mattwilliamson/fennee/models/SpotMicroESP32_with_reinforced_shoulders_4937631/images/featured_preview_RearCAD1.png

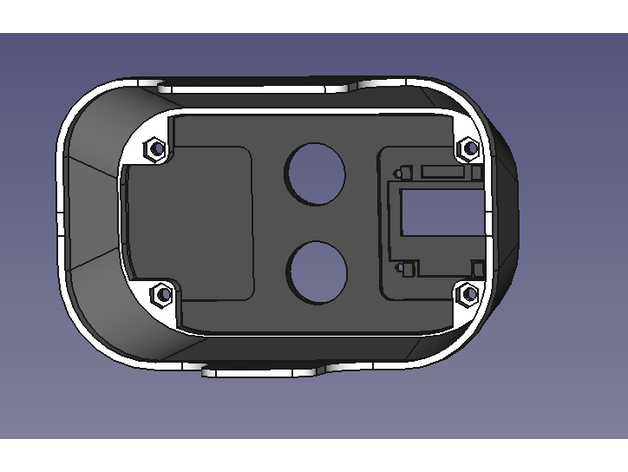
models/SpotMicroESP32_with_reinforced_shoulders_4937631/images/featured_preview_RearCAD1.png
