mattwilliamson/fennee/models/SpotMicroESP32_with_reinforced_shoulders_4937631/images/featured_preview_standing_with_shoulders_rear.png

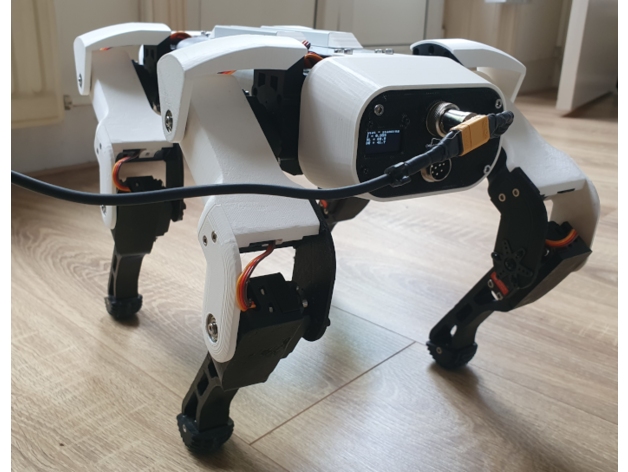
models/SpotMicroESP32_with_reinforced_shoulders_4937631/images/featured_preview_standing_with_shoulders_rear.png
