mattwilliamson/fennee/models/SpotMicroESP32_with_reinforced_shoulders_4937631/images/Shoulder_Cover.png

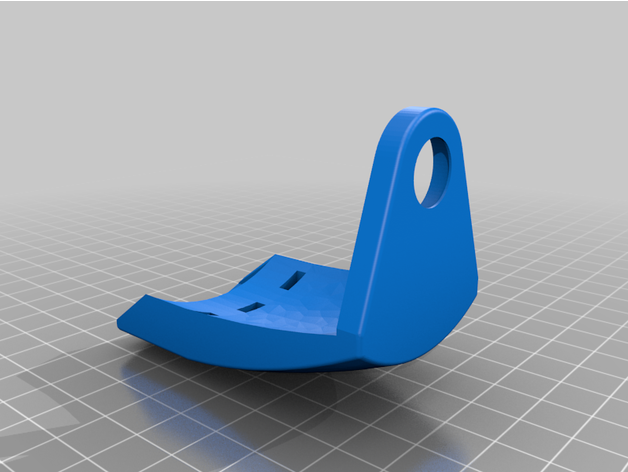
models/SpotMicroESP32_with_reinforced_shoulders_4937631/images/Shoulder_Cover.png
