mattwilliamson/fennee/models/SpotMicroESP32_with_reinforced_shoulders_4937631/images/Shoulder_Joint_Ball_Bearing_Pin_M3x8.png

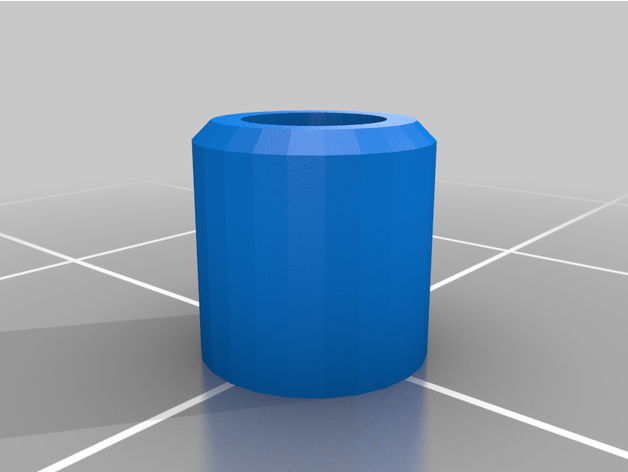
models/SpotMicroESP32_with_reinforced_shoulders_4937631/images/Shoulder_Joint_Ball_Bearing_Pin_M3x8.png
