mattwilliamson/fennee/models/SpotMicroESP32_with_reinforced_shoulders_4937631/images/Shoulder_Joint_Servo_Cap_Extended.png

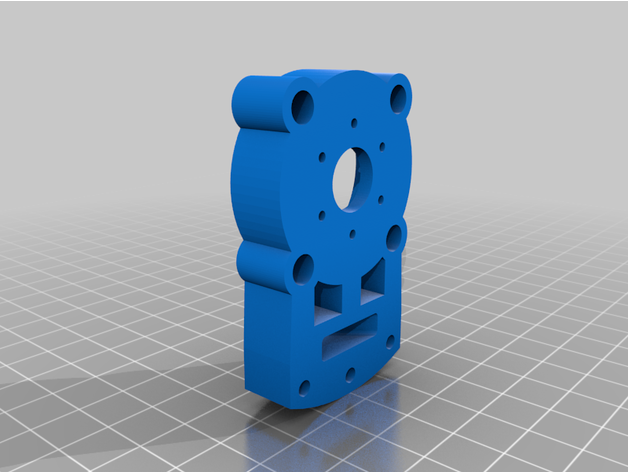
models/SpotMicroESP32_with_reinforced_shoulders_4937631/images/Shoulder_Joint_Servo_Cap_Extended.png
