mattwilliamson/fennee/models/SpotMicroESP32_with_reinforced_shoulders_4937631/images/Shoulder_Joint_Servomount_extended_BB.png

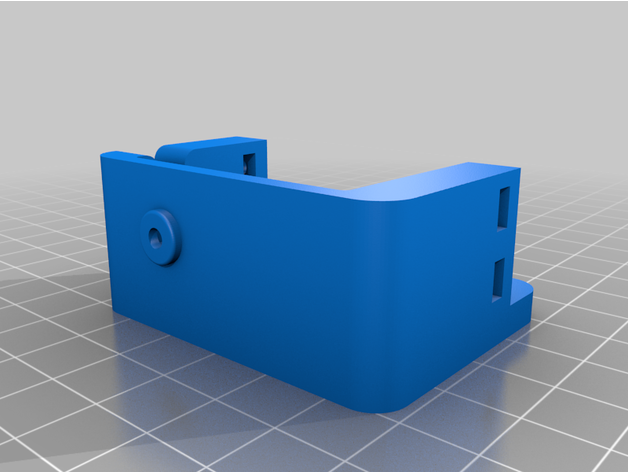
models/SpotMicroESP32_with_reinforced_shoulders_4937631/images/Shoulder_Joint_Servomount_extended_BB.png
