mattwilliamson/fennee/models/Rear_Cover/Rear_Cover_Shell_Medium.FCStd

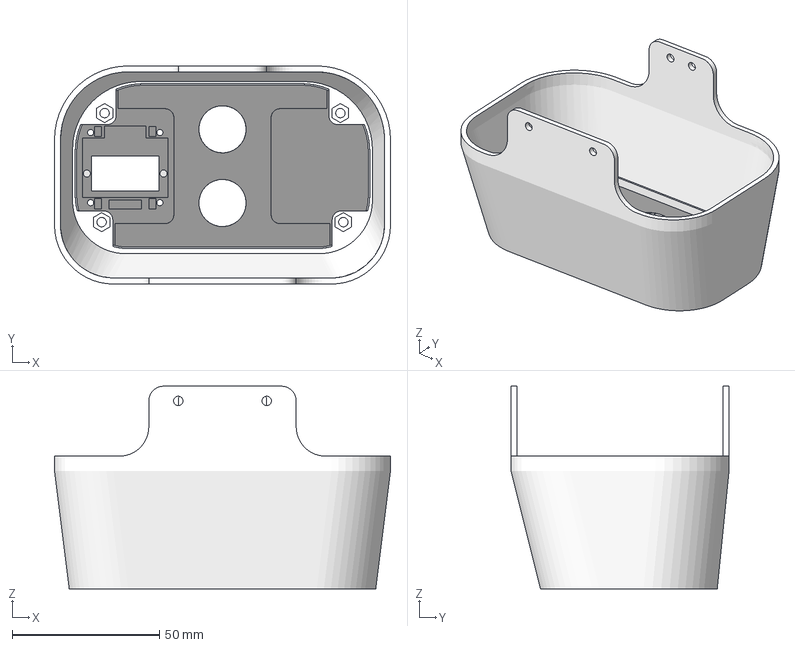
[picture p30: CAD file, 2023-06-12]
models/Rear_Cover/Rear_Cover_Shell_Medium.FCStd
114.0 x 74.0 x 68.7 mm
Rear_Cover_Shell_medium
Rear_Cover_Plate_medium
Power Plug Hole (Meshed)
