mattwilliamson/fennee/models/SpotMicroESP32_with_reinforced_shoulders_4937631/files/Shoulder_Joint_Servomount_extended_BB.stl

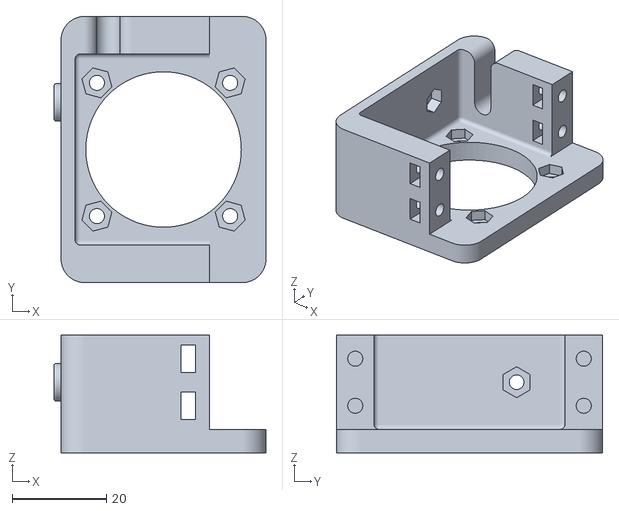
[picture p31: CAD file, 2023-05-03]
models/SpotMicroESP32_with_reinforced_shoulders_4937631/files/Shoulder_Joint_Servomount_extended_BB.stl
45.0 x 56.5 x 25.0
