mattwilliamson/fennee/models/top_cover/top_cover_back.stl

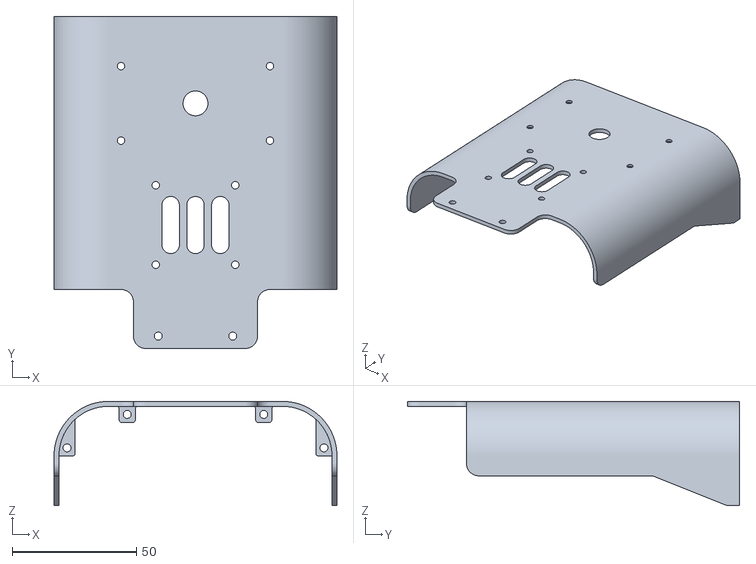
[picture p32: CAD file, 2023-05-14]
models/top_cover/top_cover_back.stl
114.0 x 133.8 x 42.0
