mattwilliamson/fennee/models/Wrist_35kg_servo/Wrist.FCStd

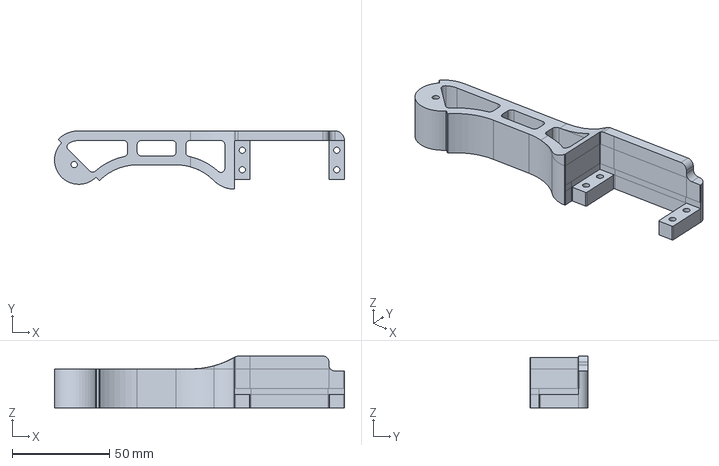
[picture p33: CAD file, 2023-06-16]
models/Wrist_35kg_servo/Wrist.FCStd
149.0 x 30.0 x 26.6 mm
