mattwilliamson/fennee/fennee_description/meshes/FreeCAD/SpotMicroAI_Bottom.FCStd

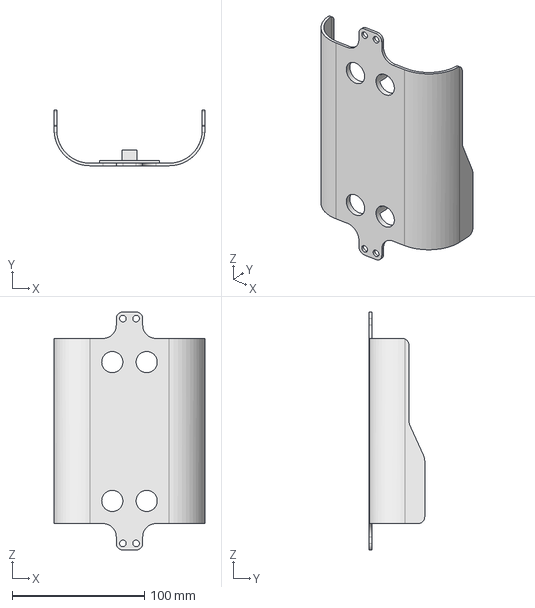
[picture p34: CAD file, 2023-04-16]
fennee_description/meshes/FreeCAD/SpotMicroAI_Bottom.FCStd
114.0 x 42.0 x 180.0 mm
