mattwilliamson/fennee/models/face/Front_Cover_oakdlite.FCStd

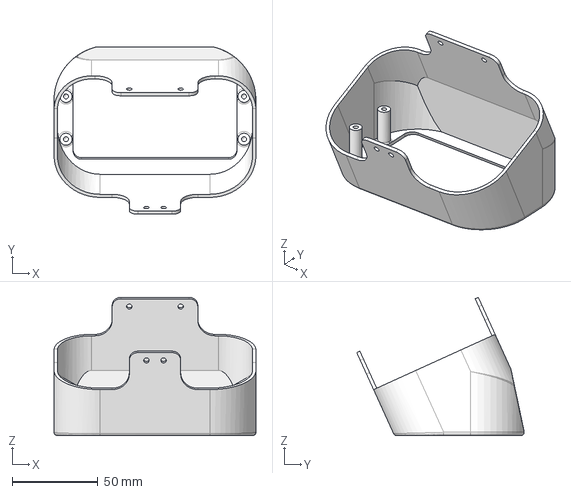
[picture p35: CAD file, 2023-05-17]
models/face/Front_Cover_oakdlite.FCStd
118.0 x 97.8 x 80.8 mm
