mattwilliamson/fennee/models/Rear_Cover/Rear_Cover_Plate_Medium.stl

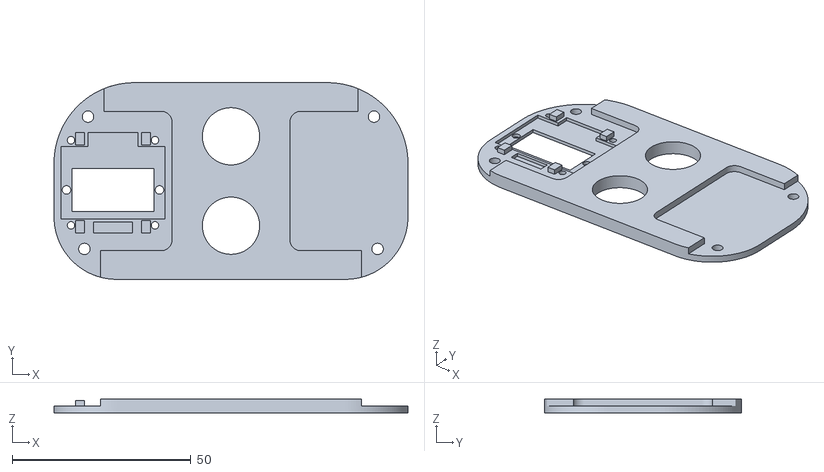
[picture p36: CAD file, 2023-06-12]
models/Rear_Cover/Rear_Cover_Plate_Medium.stl
99.0 x 55.0 x 4.00
