mattwilliamson/fennee/models/SpotMicroESP32_with_reinforced_shoulders_4937631/files/Shoulder_Joint_Servo_Cap_Extended.stl

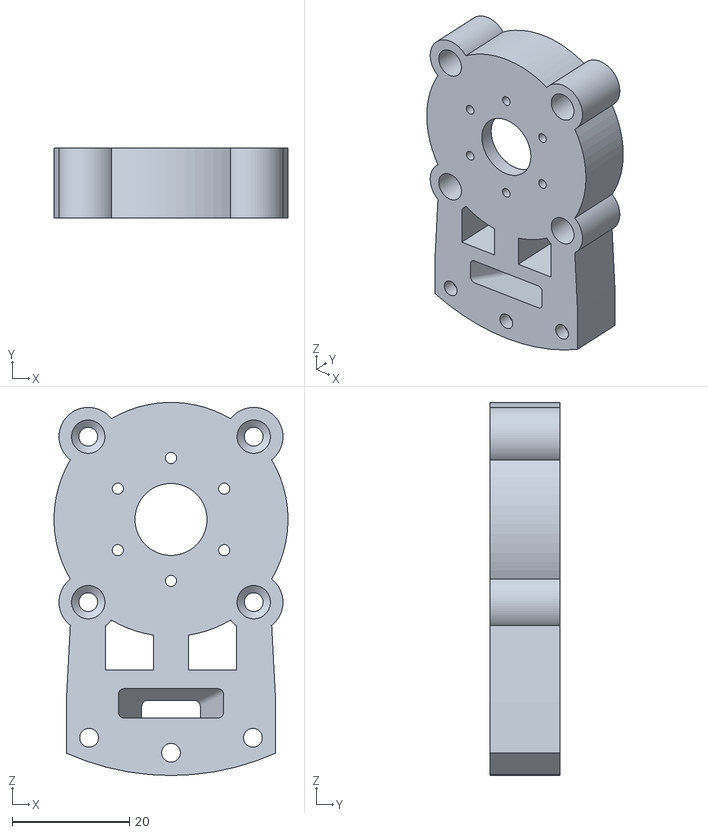
[picture p37: CAD file, 2023-05-03]
models/SpotMicroESP32_with_reinforced_shoulders_4937631/files/Shoulder_Joint_Servo_Cap_Extended.stl
40.0 x 12.0 x 63.8
