mattwilliamson/fennee/models/top_cover/top_cover_front.stl

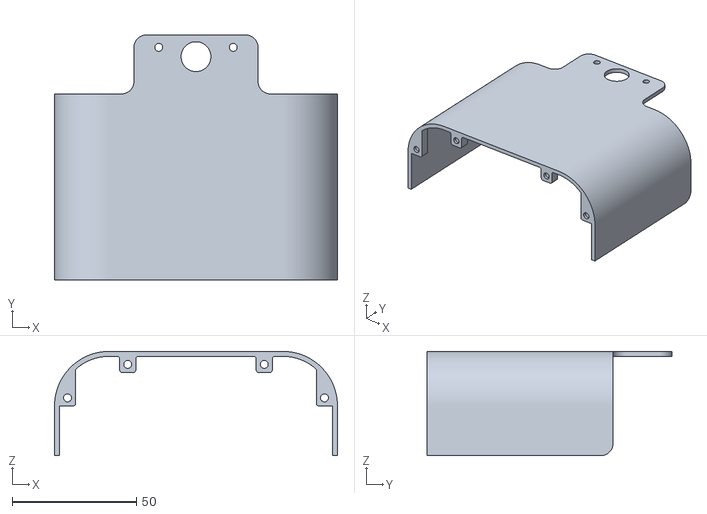
[picture p38: CAD file, 2023-05-14]
models/top_cover/top_cover_front.stl
114.0 x 98.8 x 42.0
