mattwilliamson/fennee/fennee_description/meshes/FreeCAD/SpotMicroAI_Top.FCStd

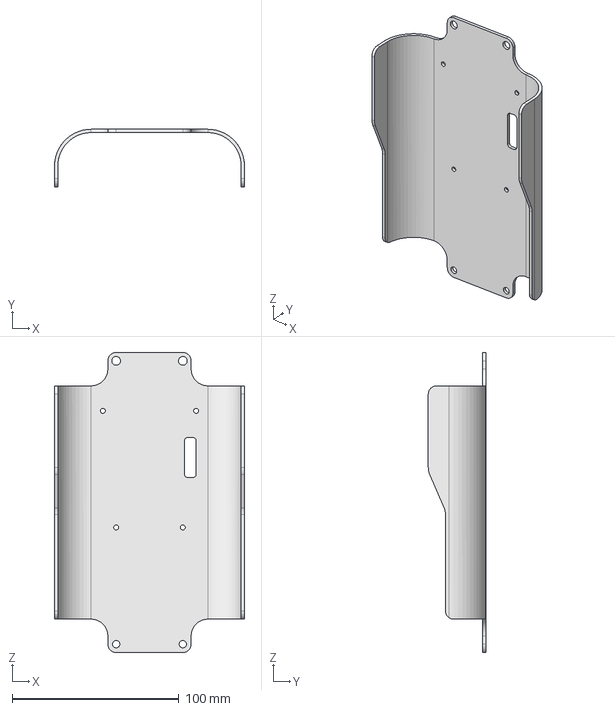
[picture p39: CAD file, 2023-04-16]
fennee_description/meshes/FreeCAD/SpotMicroAI_Top.FCStd
114.0 x 34.5 x 180.0 mm
