mattwilliamson/fennee/fennee_description/meshes/stl/R_side_plate.stl

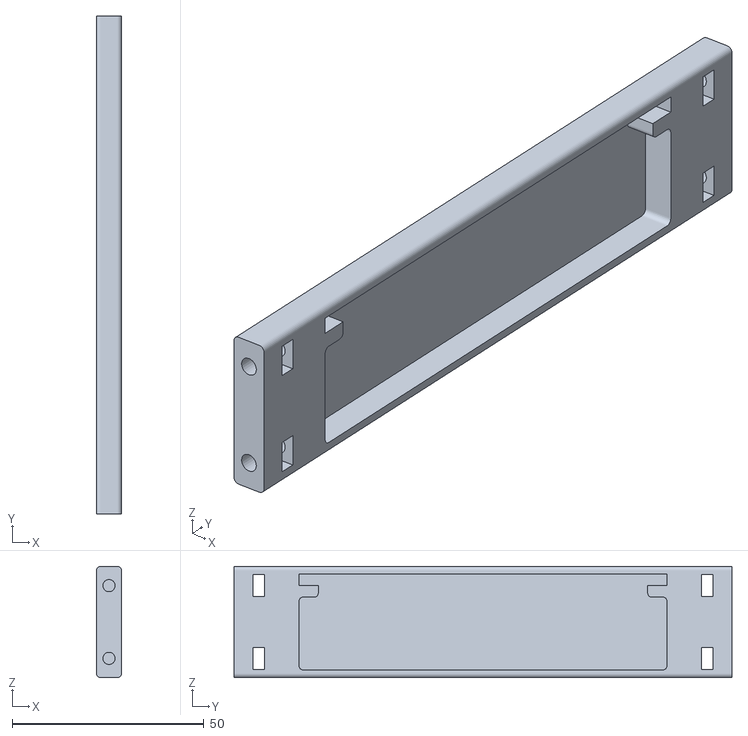
[picture p40: CAD file, 2023-04-16]
fennee_description/meshes/stl/R_side_plate.stl
6.50 x 130.0 x 29.0
