mattwilliamson/fennee/models/SpotMicroESP32_with_reinforced_shoulders_4937631/files/Rear_Cover_Shell_Medium.FCStd

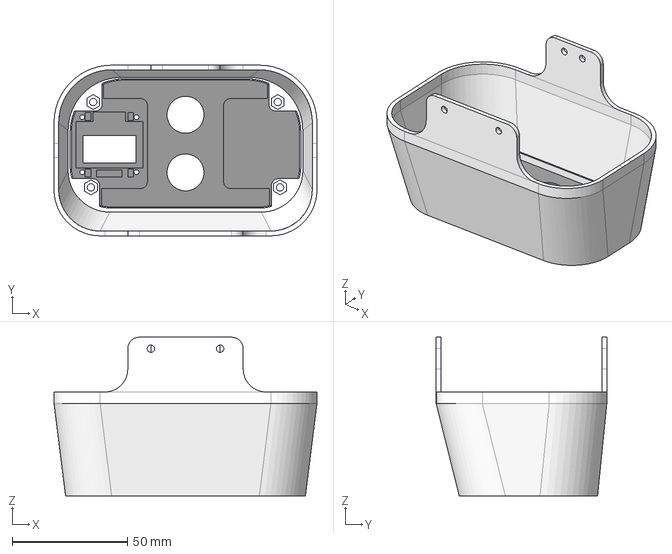
[picture p41: CAD file, 2023-05-03]
models/SpotMicroESP32_with_reinforced_shoulders_4937631/files/Rear_Cover_Shell_Medium.FCStd
114.0 x 74.0 x 68.7 mm
Rear_Cover_Shell_medium
Rear_Cover_Plate_medium
