mattwilliamson/fennee/fennee_description/meshes/FreeCAD/SpotMicroAI_AdditionalParts.FCStd

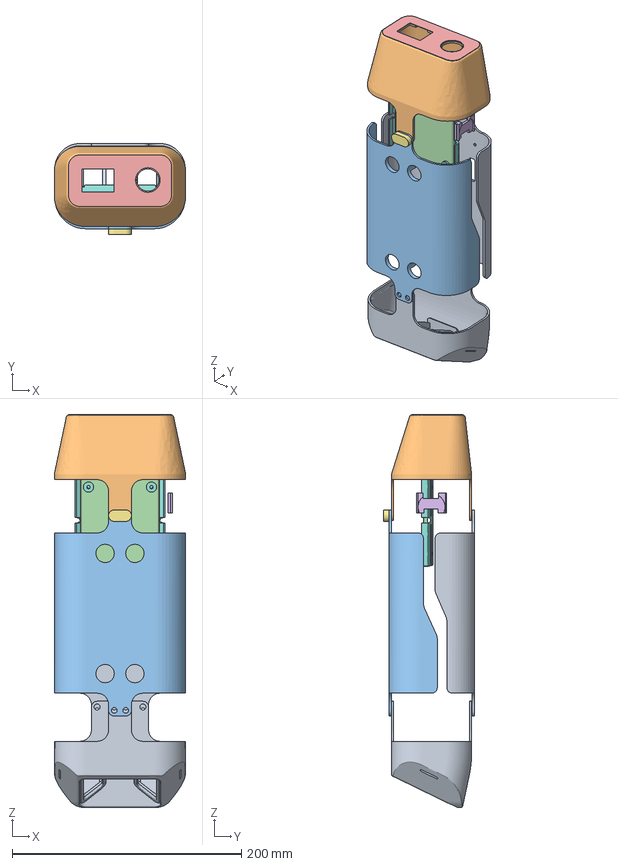
[picture p42: CAD file, 2023-04-16]
fennee_description/meshes/FreeCAD/SpotMicroAI_AdditionalParts.FCStd
114.8 x 79.5 x 343.2 mm
Top
Rear
Bottom
BatteryHolderHolder
rearlabel
LEDMount
ScrewGuard
F_cover
