mattwilliamson/fennee/fennee_description/meshes/stl/frontpart.stl

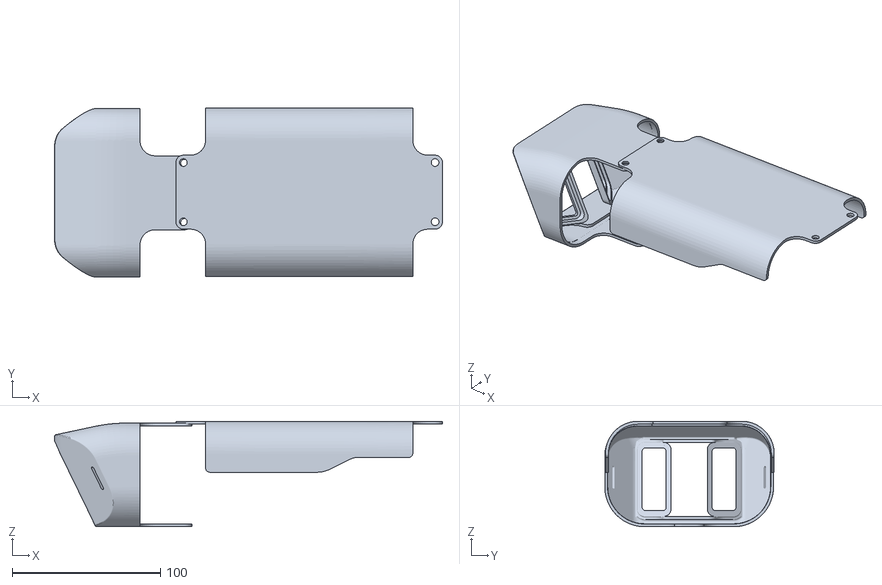
[picture p43: CAD file, 2023-04-16]
fennee_description/meshes/stl/frontpart.stl
262.0 x 114.5 x 71.2
