mattwilliamson/fennee/models/SpotMicroESP32_with_reinforced_shoulders_4937631/files/Shoulder_Joint_Ball_Bearing_Pin_M3x8.stl

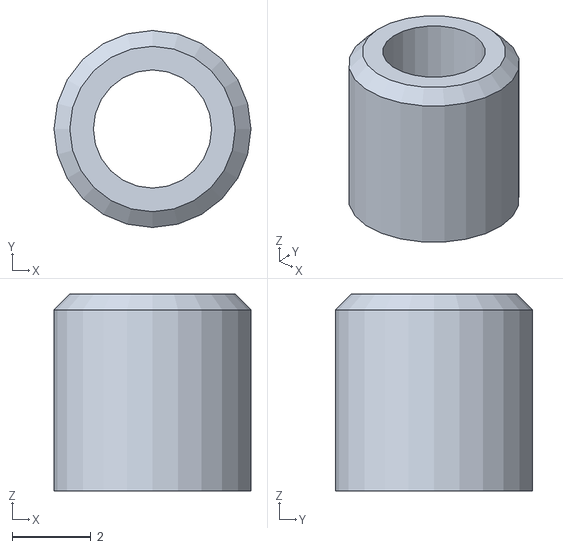
[picture p44: CAD file, 2023-05-03]
models/SpotMicroESP32_with_reinforced_shoulders_4937631/files/Shoulder_Joint_Ball_Bearing_Pin_M3x8.stl
5.00 x 5.00 x 5.00
