mattwilliamson/fennee/fennee_description/meshes/FreeCAD/SpotMicroAI_JetsonParts.FCStd

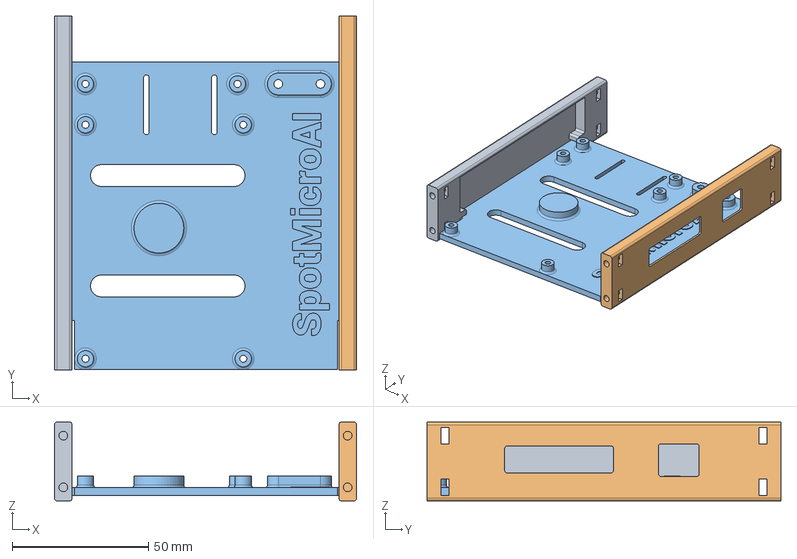
[picture p45: CAD file, 2023-04-16]
fennee_description/meshes/FreeCAD/SpotMicroAI_JetsonParts.FCStd
111.0 x 130.0 x 29.0 mm
rightSideplate
leftSideplate
JetsonPlateWithText
