mattwilliamson/fennee/fennee_description/meshes/stl/R_wrist.stl

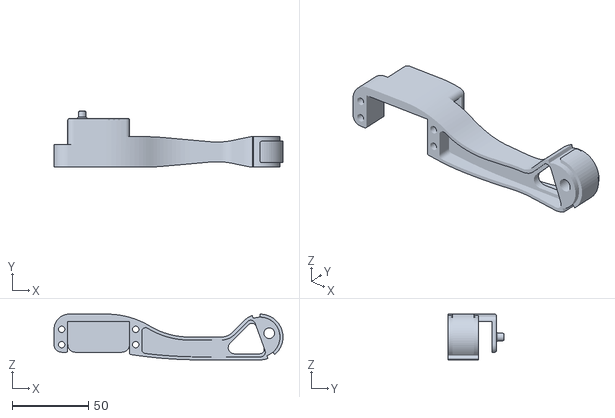
[picture p46: CAD file, 2023-04-16]
fennee_description/meshes/stl/R_wrist.stl
150.0 x 36.9 x 30.0
