mattwilliamson/fennee/fennee_description/meshes/stl/non-mega_T_cover.stl

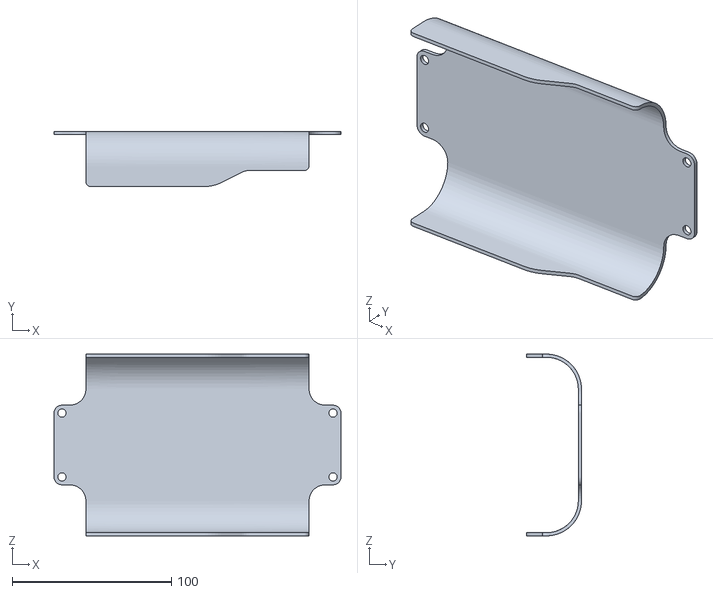
[picture p47: CAD file, 2023-04-16]
fennee_description/meshes/stl/non-mega_T_cover.stl
180.0 x 34.5 x 114.0
