mattwilliamson/fennee/models/SpotMicroESP32_with_reinforced_shoulders_4937631/files/Limb_Top_Shell_with_BB_hole.stl

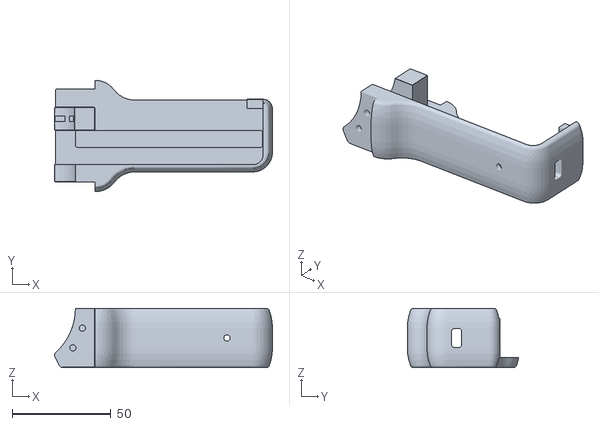
[picture p48: CAD file, 2023-05-03]
models/SpotMicroESP32_with_reinforced_shoulders_4937631/files/Limb_Top_Shell_with_BB_hole.stl
110.6 x 56.5 x 30.0
