mattwilliamson/fennee/models/SpotMicroESP32_with_reinforced_shoulders_4937631/files/Shoulder_Cover.stl

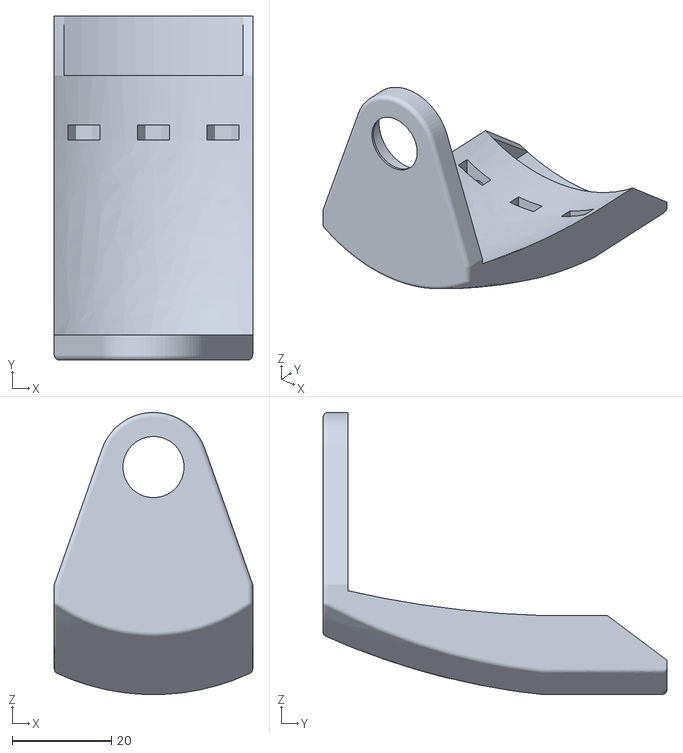
[picture p49: CAD file, 2023-05-03]
models/SpotMicroESP32_with_reinforced_shoulders_4937631/files/Shoulder_Cover.stl
40.0 x 69.3 x 56.8
