mattwilliamson/fennee/fennee_description/meshes/stl/jetson_sidepart.stl

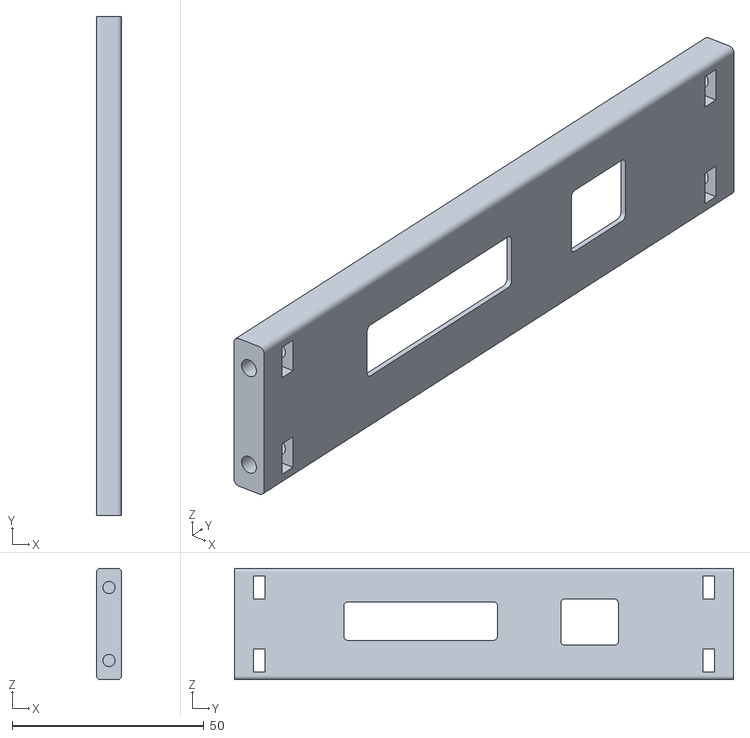
[picture p50: CAD file, 2023-04-16]
fennee_description/meshes/stl/jetson_sidepart.stl
6.50 x 130.0 x 29.0
