mattwilliamson/fennee/fennee_description/meshes/stl/lshoulder.stl

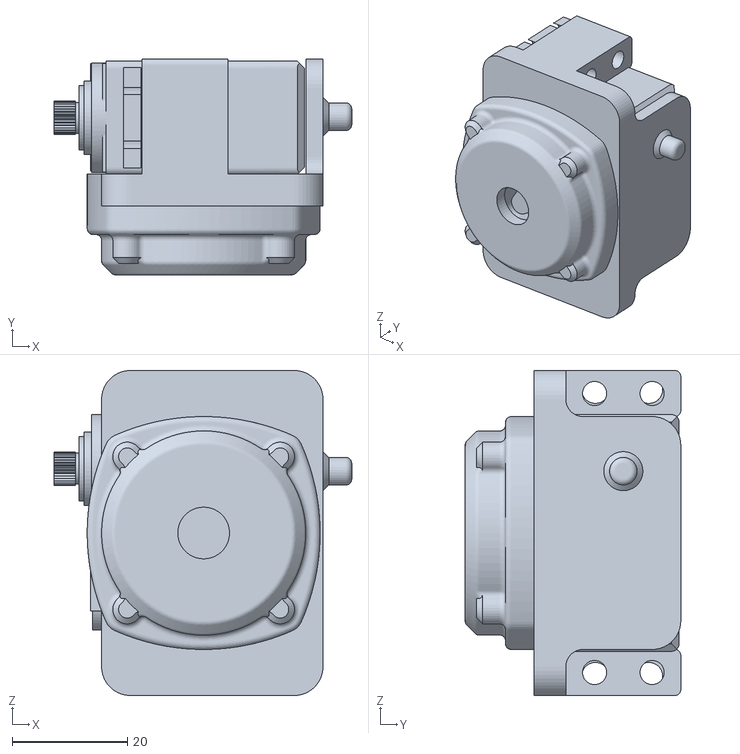
[picture p51: CAD file, 2023-04-16]
fennee_description/meshes/stl/lshoulder.stl
51.7 x 37.5 x 56.5
