mattwilliamson/fennee/fennee_description/meshes/stl/label.stl

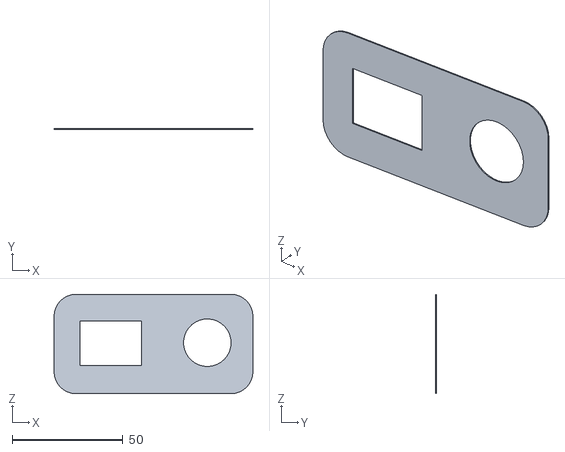
[picture p52: CAD file, 2023-04-16]
fennee_description/meshes/stl/label.stl
90.0 x 0.4 x 45.0
