mattwilliamson/fennee/fennee_description/meshes/stl/plate.stl

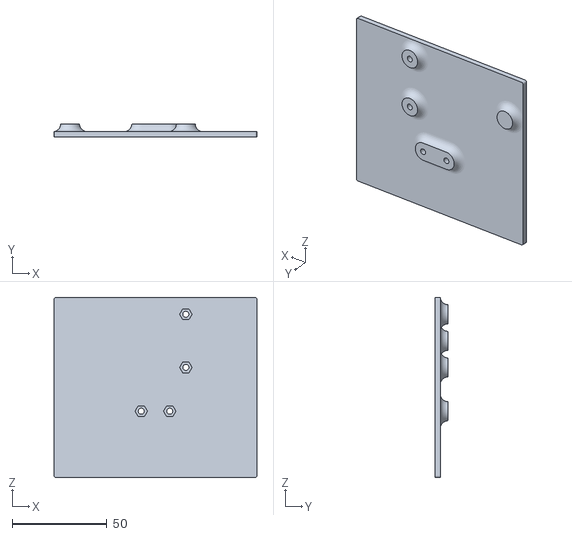
[picture p53: CAD file, 2023-04-16]
fennee_description/meshes/stl/plate.stl
107.0 x 7.00 x 95.0
