mattwilliamson/fennee/fennee_description/meshes/stl/F_cover.stl

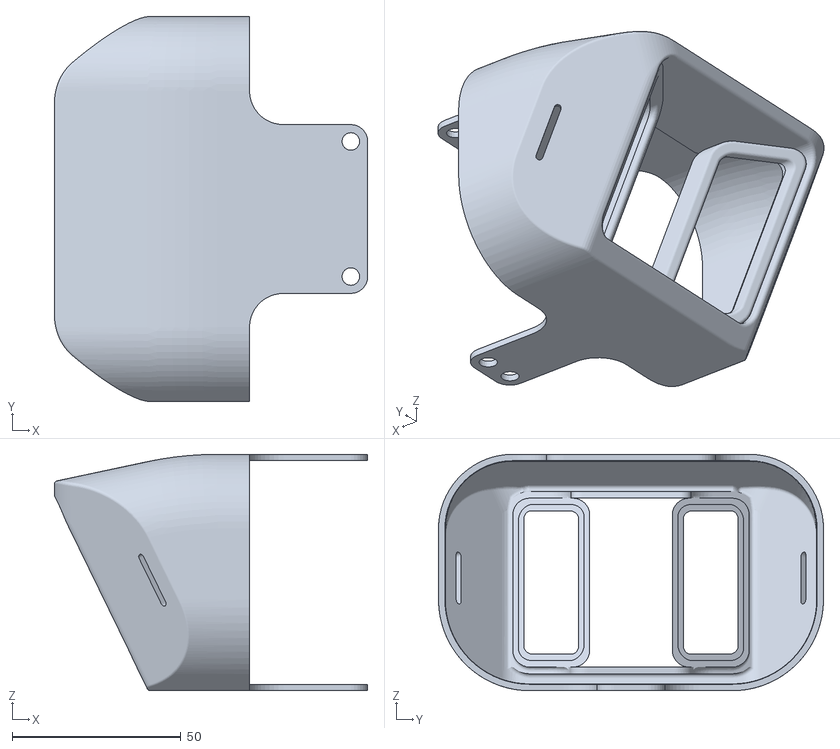
[picture p54: CAD file, 2023-04-16]
fennee_description/meshes/stl/F_cover.stl
92.8 x 114.0 x 70.0
