mattwilliamson/fennee/fennee_description/meshes/stl/R_cover.stl

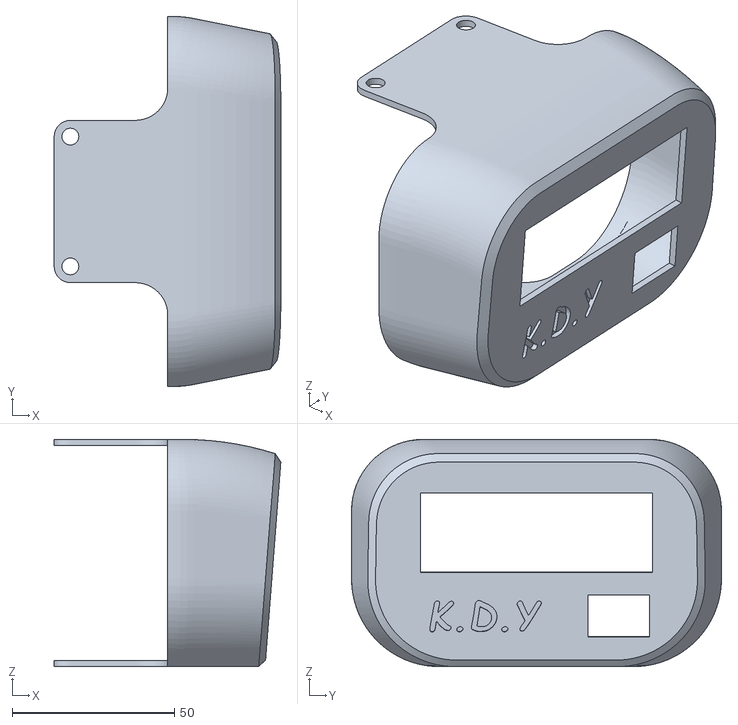
[picture p55: CAD file, 2023-04-16]
fennee_description/meshes/stl/R_cover.stl
69.8 x 114.0 x 70.0
