mattwilliamson/fennee/fennee_description/meshes/stl/ledholder.stl

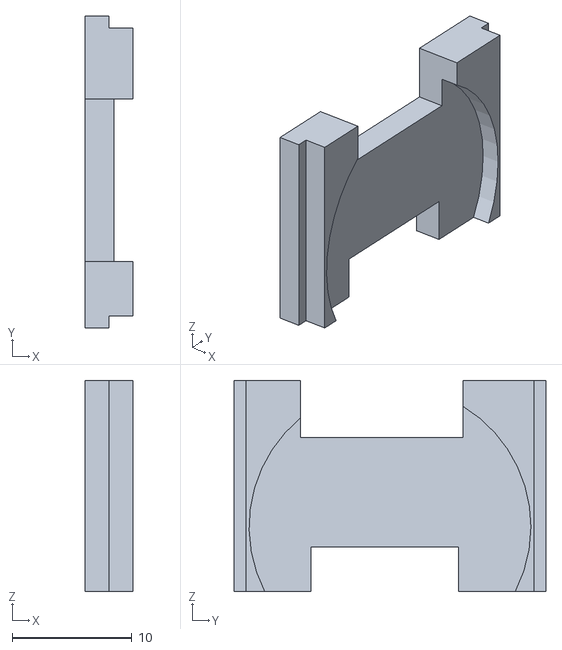
[picture p56: CAD file, 2023-04-16]
fennee_description/meshes/stl/ledholder.stl
4.00 x 26.0 x 17.6
