mattwilliamson/fennee/fennee_description/meshes/stl/F_shoulder.stl

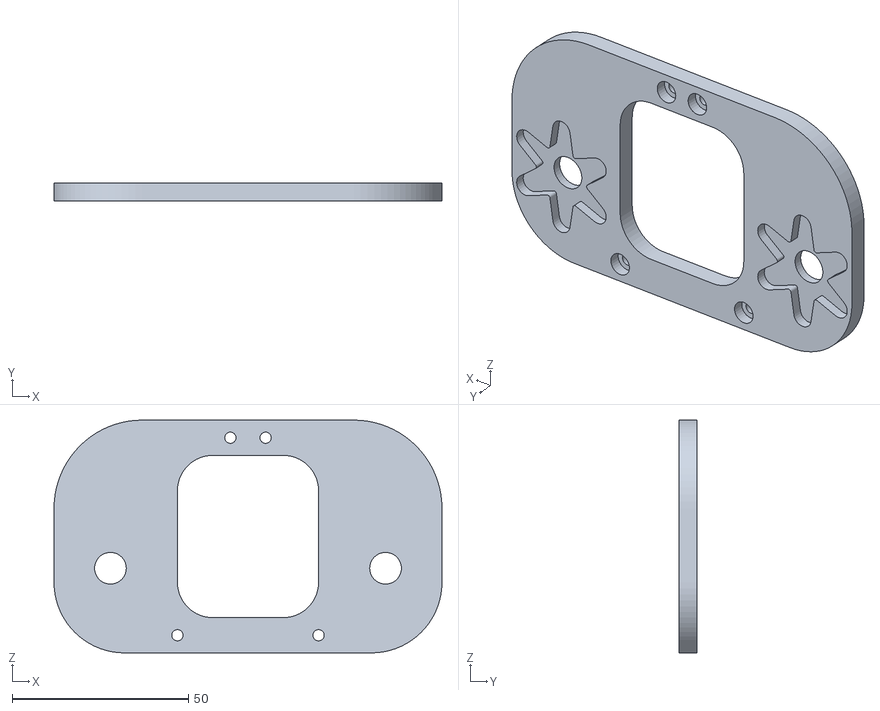
[picture p57: CAD file, 2023-04-16]
fennee_description/meshes/stl/F_shoulder.stl
110.0 x 5.00 x 66.0
