mattwilliamson/fennee/fennee_description/meshes/stl/lfoot.stl

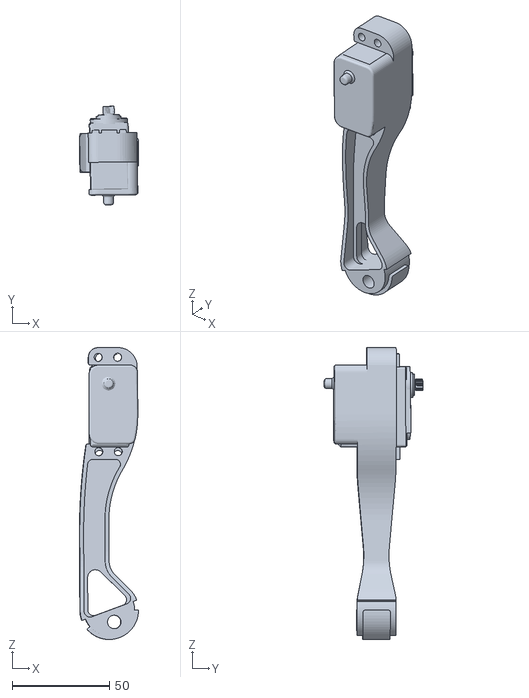
[picture p58: CAD file, 2023-04-16]
fennee_description/meshes/stl/lfoot.stl
30.4 x 50.7 x 150.0
