mattwilliamson/fennee/fennee_description/meshes/stl/batteryholder.stl

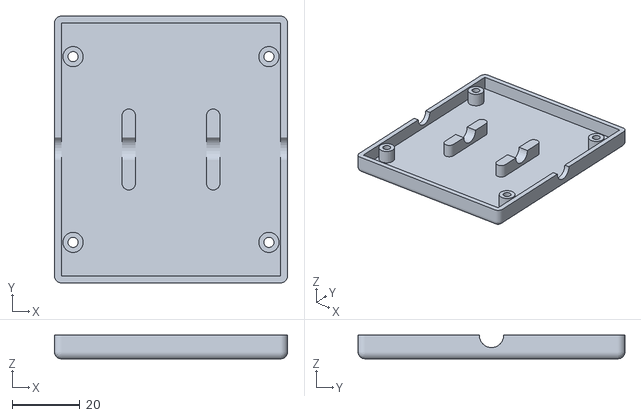
[picture p59: CAD file, 2023-04-16]
fennee_description/meshes/stl/batteryholder.stl
69.0 x 79.0 x 7.00
