mattwilliamson/fennee/fennee_description/meshes/stl/batteryholder2.stl

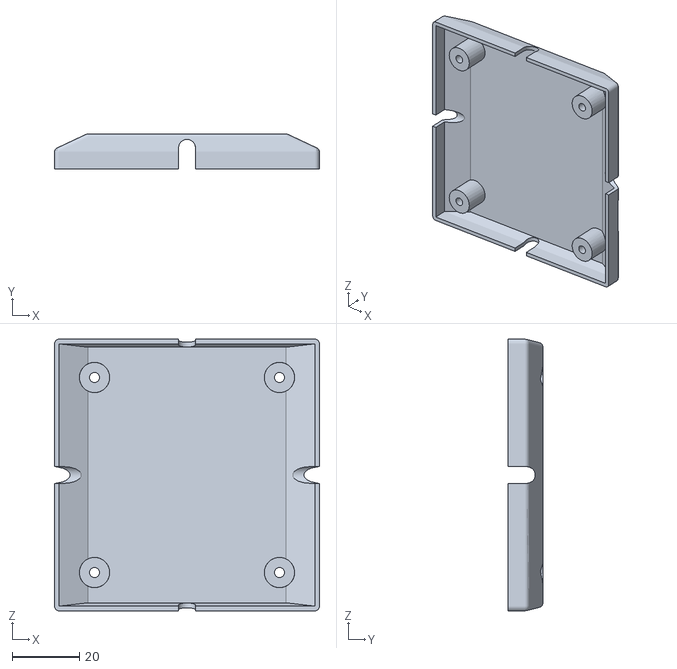
[picture p60: CAD file, 2023-04-16]
fennee_description/meshes/stl/batteryholder2.stl
78.8 x 10.4 x 80.8
