mattwilliamson/fennee/fennee_description/meshes/stl/foot.stl

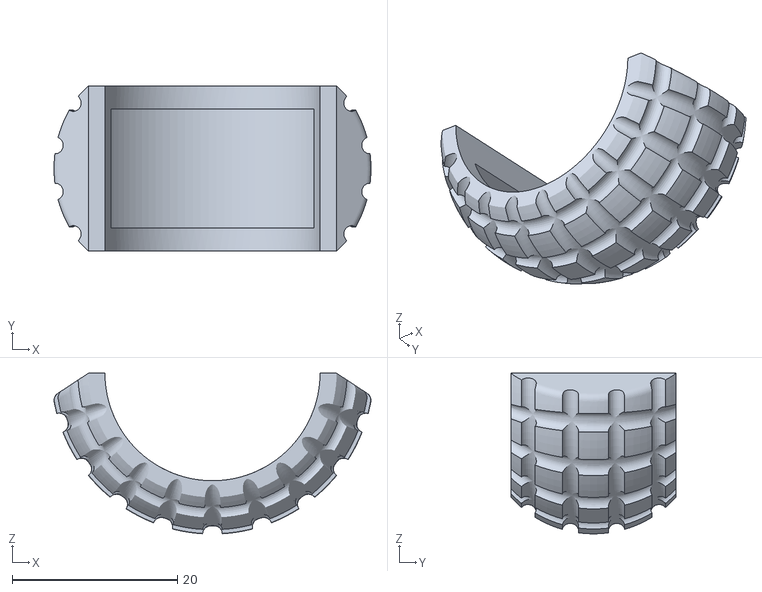
[picture p61: CAD file, 2023-04-16]
fennee_description/meshes/stl/foot.stl
38.3 x 20.0 x 19.4
