mattwilliamson/fennee/fennee_description/meshes/stl/L_arm_joint.stl

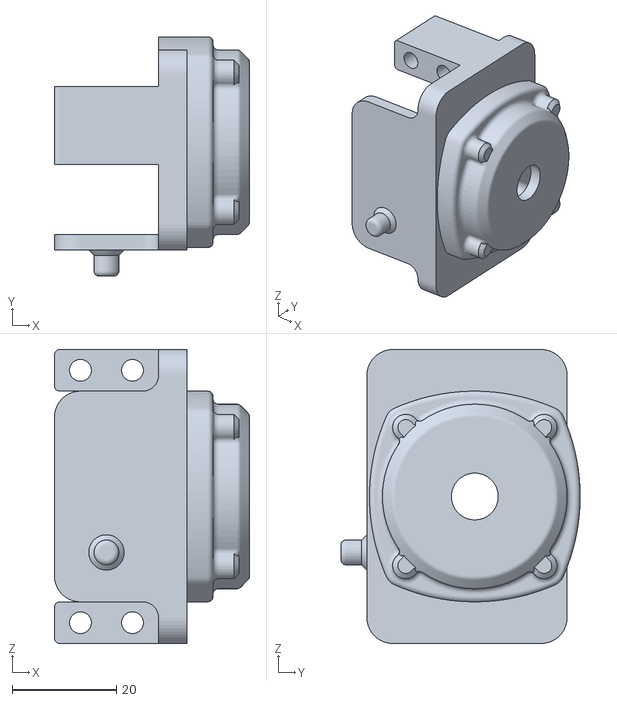
[picture p62: CAD file, 2023-04-16]
fennee_description/meshes/stl/L_arm_joint.stl
37.5 x 46.0 x 56.5
