mattwilliamson/fennee/fennee_description/meshes/stl/L_arm.stl

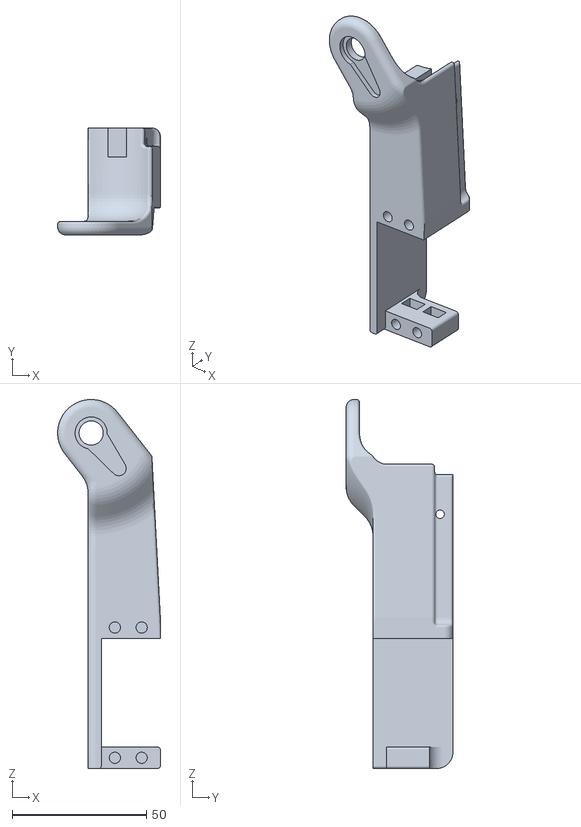
[picture p63: CAD file, 2023-04-16]
fennee_description/meshes/stl/L_arm.stl
38.2 x 39.8 x 137.4
