mattwilliamson/fennee/fennee_description/meshes/stl/rear2.stl

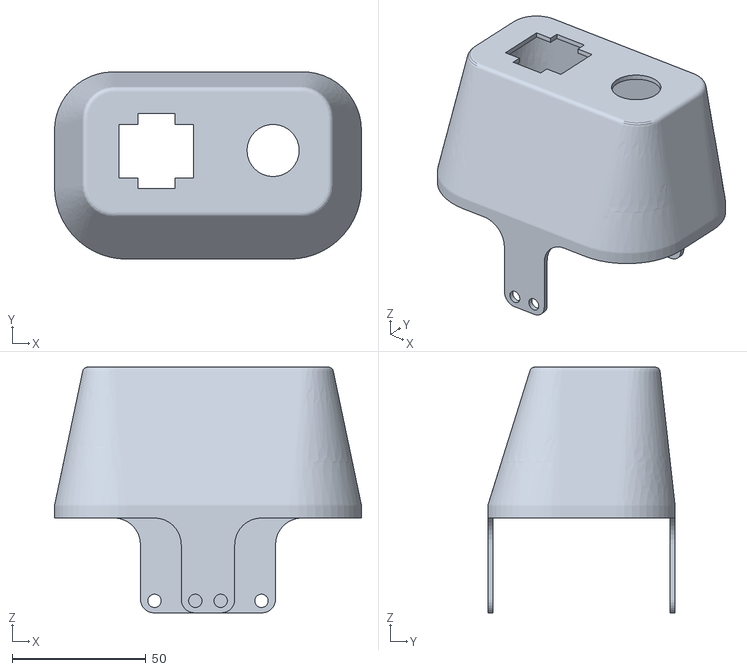
[picture p64: CAD file, 2023-04-16]
fennee_description/meshes/stl/rear2.stl
114.8 x 70.0 x 91.9
