mattwilliamson/fennee/fennee_description/meshes/stl/backpart.stl

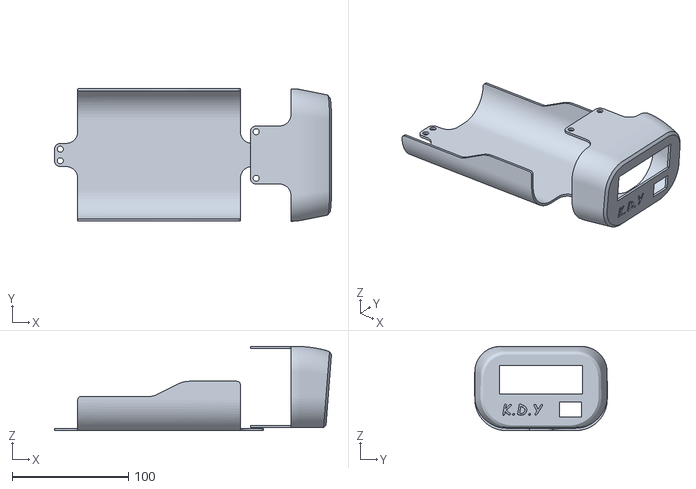
[picture p65: CAD file, 2023-04-16]
fennee_description/meshes/stl/backpart.stl
238.4 x 114.1 x 72.5
