mattwilliamson/fennee/fennee_description/meshes/stl/R_shoulder.stl

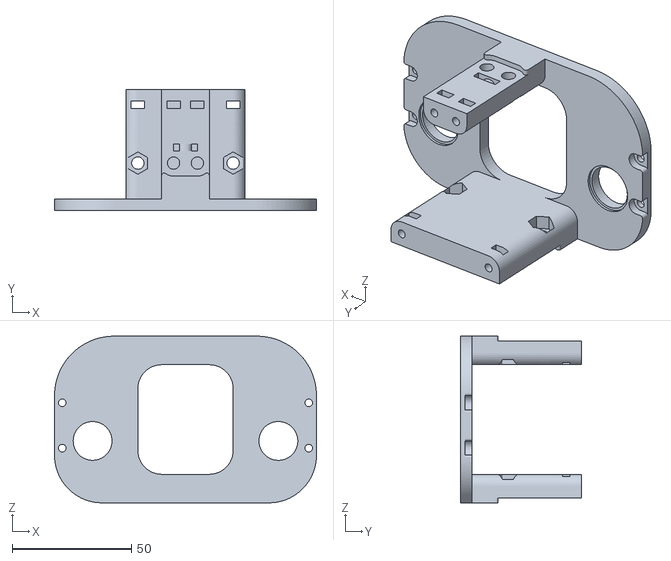
[picture p66: CAD file, 2023-04-16]
fennee_description/meshes/stl/R_shoulder.stl
110.0 x 51.0 x 70.0
