mattwilliamson/fennee/fennee_description/meshes/stl/R_arm_cover.stl

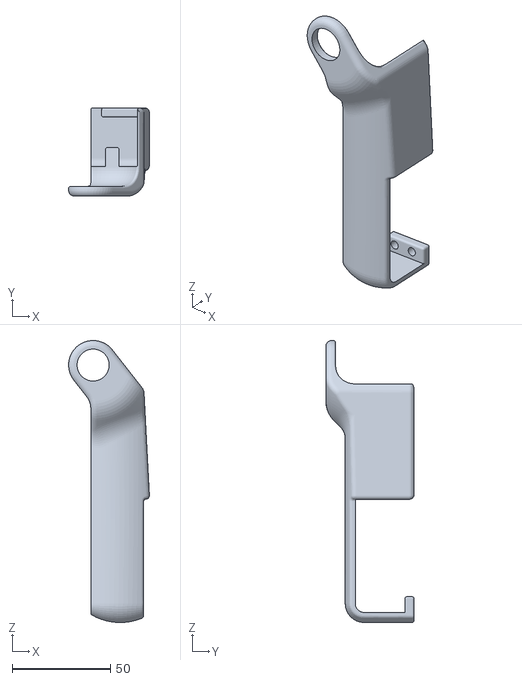
[picture p67: CAD file, 2023-04-16]
fennee_description/meshes/stl/R_arm_cover.stl
41.2 x 45.0 x 143.5
