mattwilliamson/fennee/fennee_description/meshes/stl/L_ultra_sonic.stl

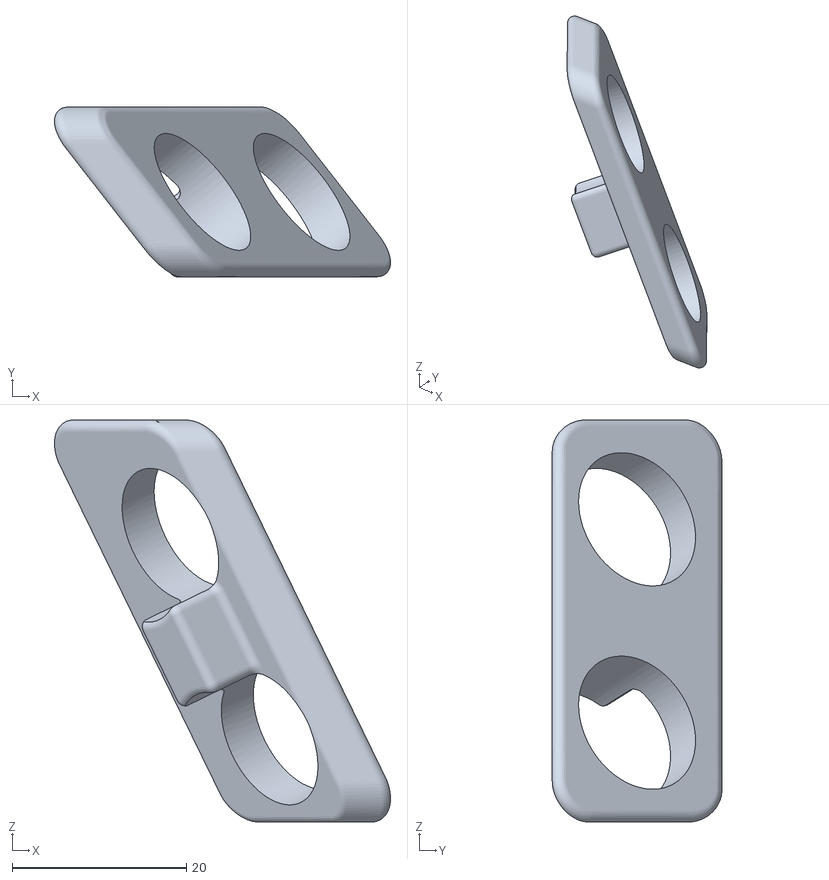
[picture p68: CAD file, 2023-04-16]
fennee_description/meshes/stl/L_ultra_sonic.stl
38.6 x 19.5 x 46.2
