mattwilliamson/fennee/fennee_description/meshes/stl/top.stl

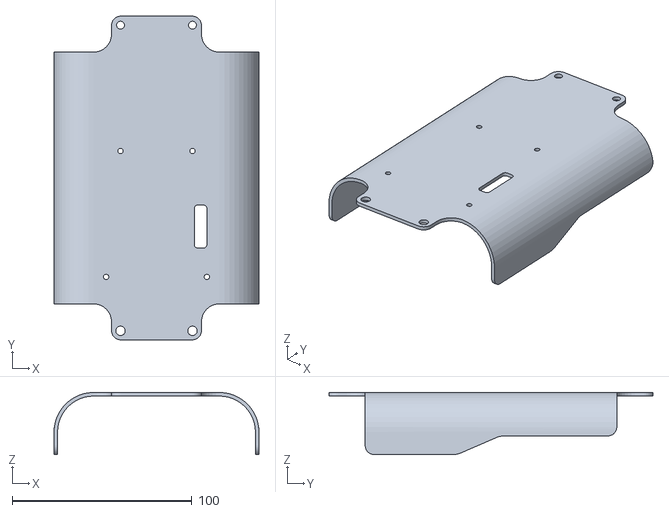
[picture p69: CAD file, 2023-04-16]
fennee_description/meshes/stl/top.stl
114.0 x 180.0 x 34.5
