mattwilliamson/fennee/fennee_description/meshes/stl/non-mega_B_cover.stl

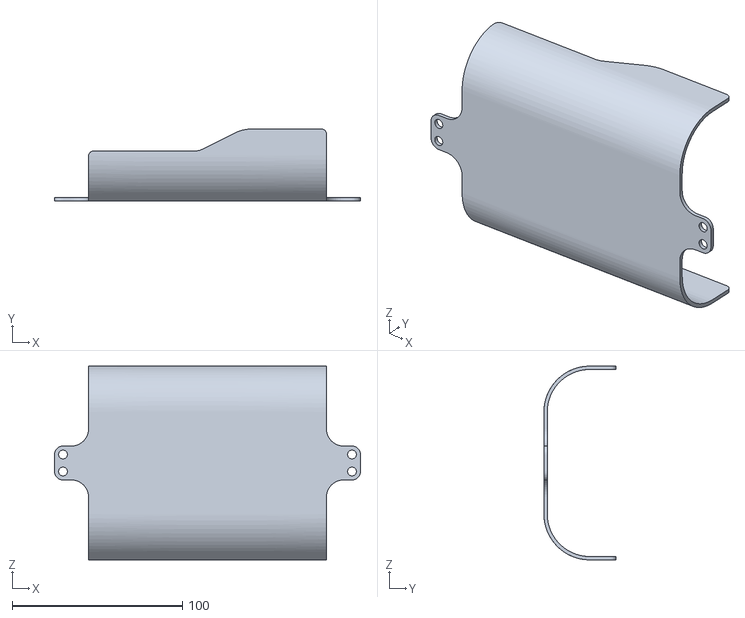
[picture p70: CAD file, 2023-04-16]
fennee_description/meshes/stl/non-mega_B_cover.stl
180.0 x 42.5 x 114.0
