mattwilliamson/fennee/fennee_description/meshes/stl/jetsonPlate.stl

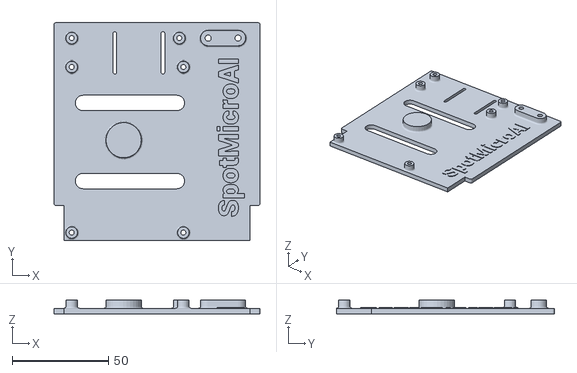
[picture p71: CAD file, 2023-04-16]
fennee_description/meshes/stl/jetsonPlate.stl
107.0 x 113.0 x 7.10
